worthleychristopher-dev/IC-Test-Fixture-Capstone/docs/eco/ECO_001.pdf

## ENGINEERING CHANGE ORDER (ECO)

ECO NO: 001 APPLIES TO: Reconfigurable Test Fixture (PCB) ECO DATE: 4/30/26
SHEET 1 OF 1

CHANGES:
1. ( Remove ): R9 (CRCW120657K6FKEA) 57.6k ohm resistor.

REASON: Incorrect Value

2. ( Add ): 6490k ohm 1% resistor (0603) to R9.

REASON: Lets circuit produce 4.5 V reference voltage.

Signature: ZF
