worthleychristopher-dev/IC-Test-Fixture-Capstone/docs/eco/ECO_002.pdf

## ENGINEERING CHANGE ORDER (ECO)

ECO NO: 002 APPLIES TO: Reconfigurable Test Fixture (PCB) ECO DATE: 4/30/26
SHEET 1 OF 1

CHANGES:
1. ( | Ignore | ): | Engraved | Reference | Voltage
Values for Vref circuits (U4, U5, U6, U7, U8, TLV431s)

REASON: Incorrect Value Engraved (Reversed Order)

Signature: ZF
