worthleychristopher-dev/IC-Test-Fixture-Capstone/docs/eco/ECO_003.pdf

## ENGINEERING CHANGE ORDER (ECO)

ECO NO: 003 APPLIES TO: Reconfigurable Test Fixture (PCB) ECO DATE: 4/30/26
SHEET 1 OF 1

CHANGES:
1. ( | Ignore | ): | Engraved | positive | polarity
symbol for D3 and D4 (SMF5.0A) components.

REASON: Incorrect polarity orientation engraved.

Signature: ZF
