worthleychristopher-dev/IC-Test-Fixture-Capstone/docs/eco/ECO_004.pdf

## ENGINEERING CHANGE ORDER (ECO)

ECO NO: 004 APPLIES TO: Reconfigurable Test Fixture (PCB) ECO DATE: 4/30/26
SHEET 1 OF 2

CHANGES:
1. ( Add ): Solder 30 gauge AWG jumper wire from USBGND of C1 to GND_ISO of C4

REASON: Isolated circuit unstable without shorted grounds.

Signature: ZF

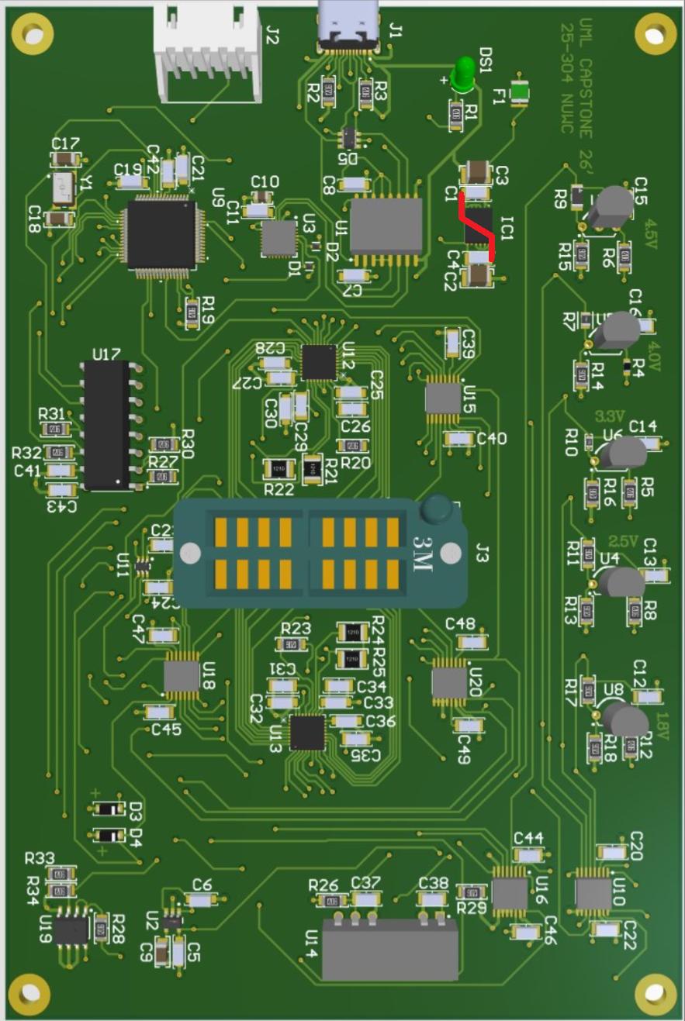
[picture p35: figure]
