worthleychristopher-dev/IC-Test-Fixture-Capstone/docs/eco/ECO_005.pdf

## ENGINEERING CHANGE ORDER (ECO)

ECO NO: 005 APPLIES TO: Reconfigurable Test Fixture (PCB) ECO DATE: 4/30/26
SHEET 1 OF 2

CHANGES:
1. ( Cut ): Traces for pins 6, 7, 10, & 11 of U1 (ADUM4160BRWZ)

REASON: Upstream & Downstream pins routed incorrectly.

2. ( Add ): 30 Gauge AWG jumper wire to connect Pin 3 of D5 to Pin 7 of U1.
3. ( Add ): 30 Gauge AWG jumper wire to connect Pin 4 of D5 to Pin 6 of U1.
4. ( Add ): 30 Gauge AWG jumper wire to connect Pin 10 of U1 to Pin 4 of U3 (CP2102-GM)
5. ( Add ): 30 Gauge AWG jumper wire to connect Pin 11 of U1 to Pin 5 of U3 (CP2102-GM)

REASON: Corrects data pathing for Upstream &
Downstream | pins | of | the | ADUM4160BRWZ | Data
isolator.

Signature: ZF

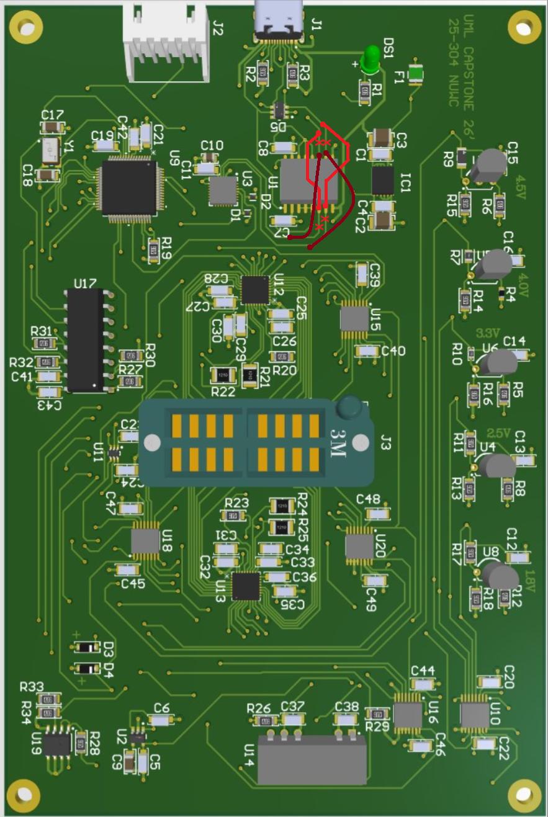
[picture p36: figure]
