worthleychristopher-dev/IC-Test-Fixture-Capstone/docs/images/hardware_images/spice_images/3_3v_TLV431_E192.png

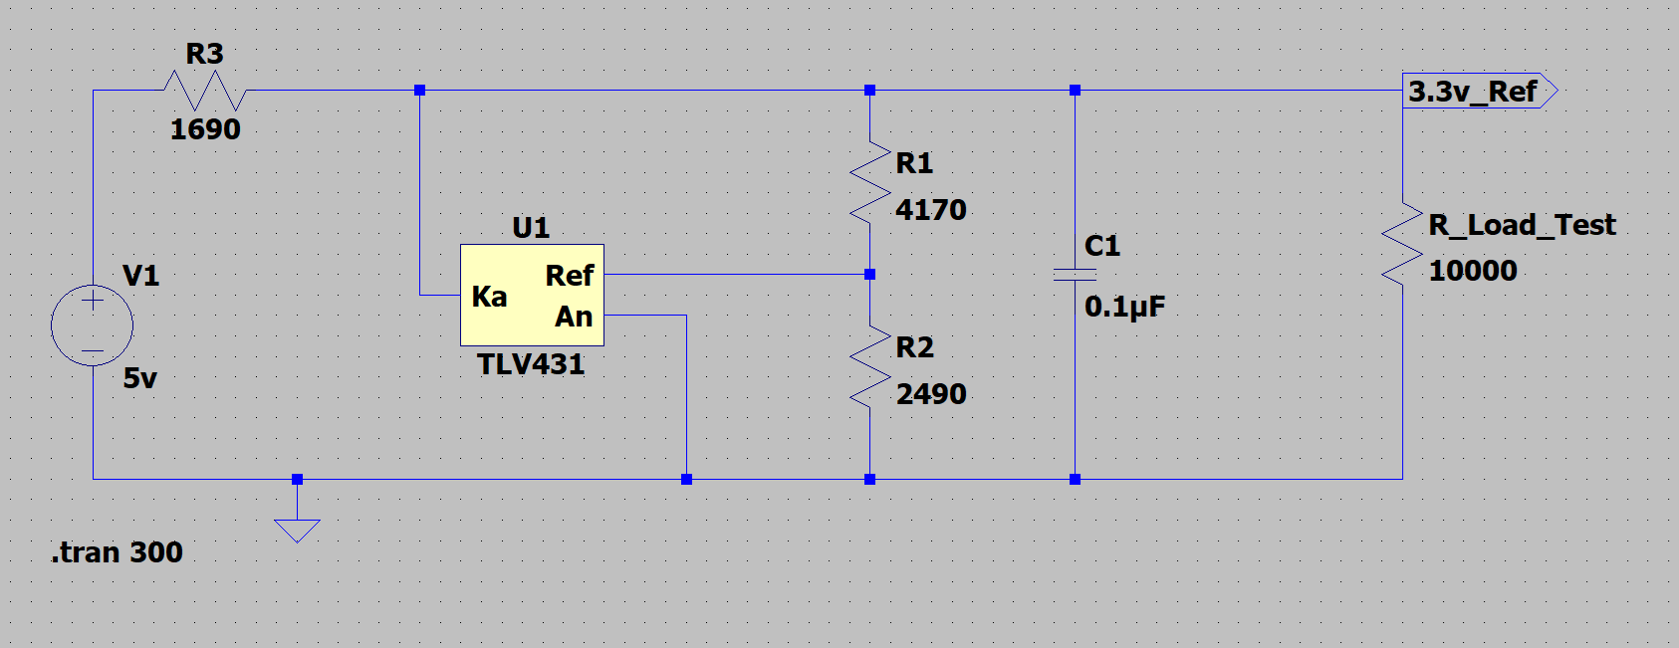
docs/images/hardware_images/spice_images/3_3v_TLV431_E192.png
