worthleychristopher-dev/IC-Test-Fixture-Capstone/docs/images/software_images/flowcharts.png

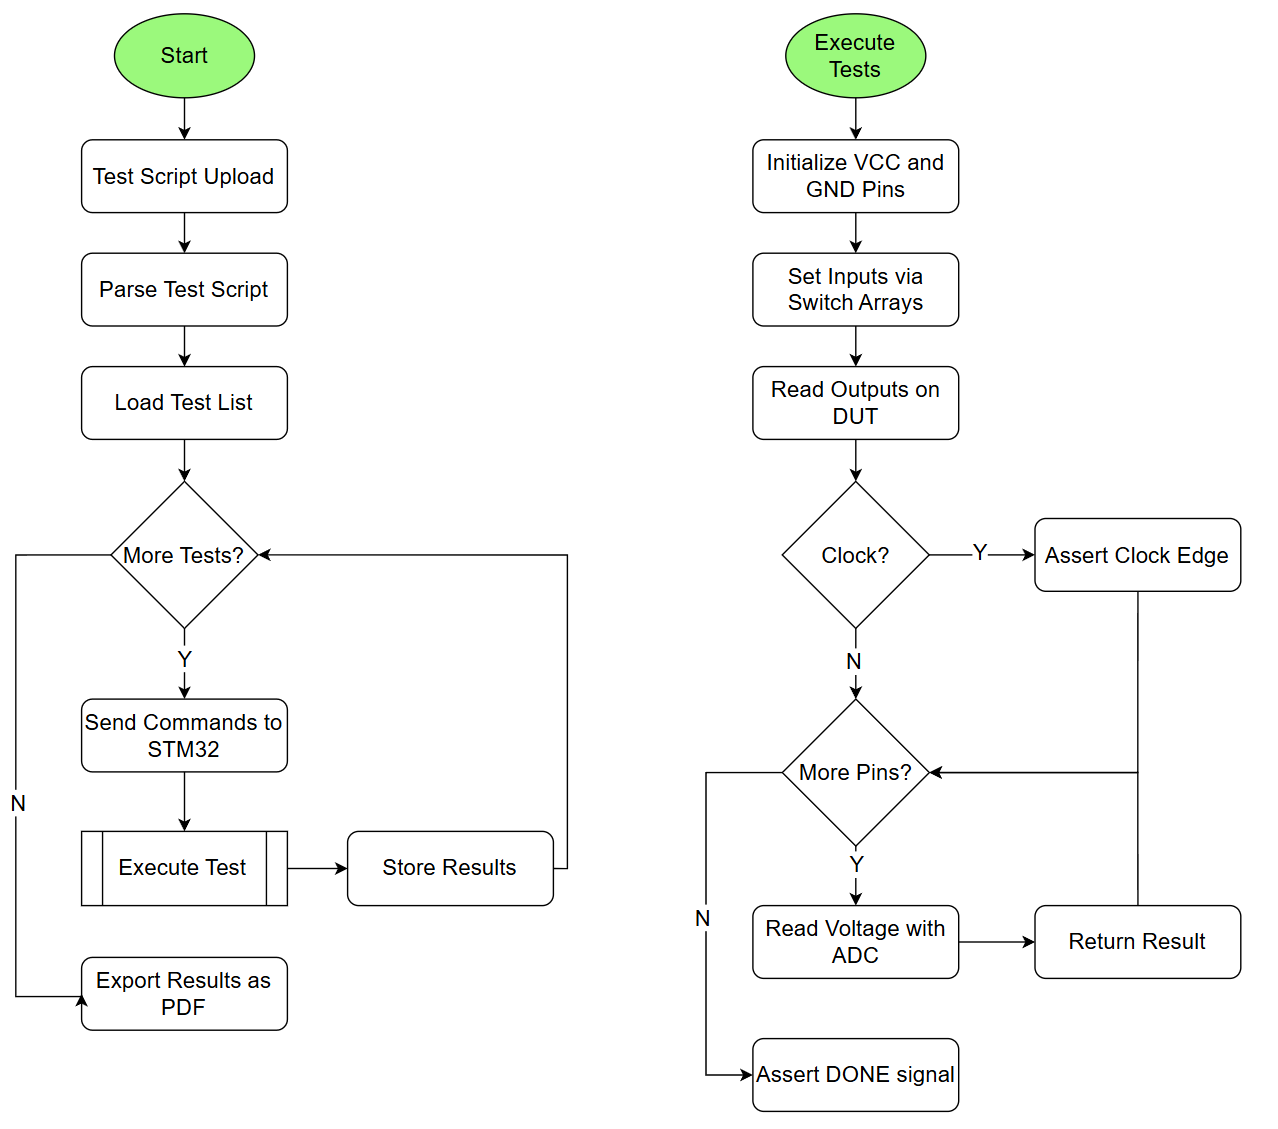
docs/images/software_images/flowcharts.png
