worthleychristopher-dev/IC-Test-Fixture-Capstone/test_results/hct_results/74hct283_short.pdf

## Pin Map

Pin Name | Pin | Pin Name | Pin
S1 | 1 | B1 | 2
A1 | 3 | S0 | 4
A0 | 5 | B0 | 6
CIN | 7 | COUT | 13
S3 | 14 | B3 | 15
A3 | 16 | S2 | 17
A2 | 18 | B2 | 19

## Global Parameters

Parameter | Value
VCC Pin | 20
GND Pin | 8
VCC Voltage | 5
Input Low | 0.8
Input High | 2
Output Low | 0.33
Output High | 3.84

## Tests: IC PASS 12/12

### A=0, B=0, CIN=0 -> S=0: PASS

Inputs | Outputs/Results
A3, A2, A1, A0 | B3, B2, B1, B0 | CIN | COUT | S3 | S2 | S1 | S0
0b0000 | 0b0000 | 0b0 | 0 | 0.0 (0) 0 | | 0.0 (0) 0 | | 0.0 (0) 0 | 0.0 (0) 0 | 0.0 (0)

### A=0, B=0, CIN=1 -> S=1: PASS

Inputs | Outputs/Results
A3, A2, A1, A0 | B3, B2, B1, B0 | CIN | COUT | S3 | S2 | S1 | S0
0b0000 | 0b0000 | 0b1 | 0 | 0.0 (0) 0 | | 0.0 (0) 0 | | 0.0 (0) 0 | 0.0 (0) 1 | 4.86 (1)

### A=1, B=0, CIN=0 -> S=1: PASS

Inputs | Outputs/Results
A3, A2, A1, A0 | B3, B2, B1, B0 | CIN | COUT | S3 | S2 | S1 | S0
0b0001 | 0b0000 | 0b0 | 0 | 0.0 (0) 0 | | 0.0 (0) 0 | | 0.0 (0) 0 | 0.0 (0) 1 | 4.86 (1)

### A=0, B=1, CIN=0 -> S=1: PASS

Inputs | Outputs/Results
A3, A2, A1, A0 | B3, B2, B1, B0 | CIN | COUT | S3 | S2 | S1 | S0
0b0000 | 0b0001 | 0b0 | 0 | 0.0 (0) 0 | | 0.0 (0) 0 | | 0.0 (0) 0 | 0.0 (0) 1 | 4.85 (1)

### A=3, B=5, CIN=0 -> S=8: PASS

Inputs | Outputs/Results
A3, A2, A1, A0 | B3, B2, B1, B0 | CIN | COUT | S3 | S2 | S1 | S0
0b0011 | 0b0101 | 0b0 | 0 | 0.0 (0) 1 | | 4.86 (1) 0 | | 0.0 (0) 0 | 0.0 (0) 0 | 0.0 (0)

### A=15, B=1, CIN=0 -> S=16: PASS

Inputs | Outputs/Results
A3, A2, A1, A0 | B3, B2, B1, B0 | CIN | COUT | S3 | S2 | S1 | S0
0b1111 | 0b0001 | 0b0 | 1 | 4.85 (1) 0 | | 0.0 (0) 0 | | 0.0 (0) 0 | 0.0 (0) 0 | 0.0 (0)

### A=15, B=15, CIN=0 -> S=30: PASS

Inputs | Outputs/Results
A3, A2, A1, A0 | B3, B2, B1, B0 | CIN | COUT | S3 | S2 | S1 | S0
0b1111 | 0b1111 | 0b0 | 1 | 4.85 (1) 1 | | 4.85 (1) 1 | | 4.85 (1) 1 | 4.85 (1) 0 | 0.0 (0)

### A=15, B=15, CIN=1 -> S=31: PASS

Inputs | Outputs/Results
A3, A2, A1, A0 | B3, B2, B1, B0 | CIN | COUT | S3 | S2 | S1 | S0
0b1111 | 0b1111 | 0b1 | 1 | 4.85 (1) 1 | | 4.85 (1) 1 | | 4.85 (1) 1 | 4.85 (1) 1 | 4.85 (1)

### A=10, B=5, CIN=0 -> S=15: PASS

Inputs | Outputs/Results
A3, A2, A1, A0 | B3, B2, B1, B0 | CIN | COUT | S3 | S2 | S1 | S0
0b1010 | 0b0101 | 0b0 | 0 | 0.0 (0) 1 | | 4.86 (1) 1 | | 4.85 (1) 1 | 4.85 (1) 1 | 4.85 (1)

### A=10, B=10, CIN=1 -> S=21: PASS

Inputs | Outputs/Results
A3, A2, A1, A0 | B3, B2, B1, B0 | CIN | COUT | S3 | S2 | S1 | S0
0b1010 | 0b1010 | 0b1 | 1 | 4.85 (1) 0 | | 0.0 (0) 1 | | 4.85 (1) 0 | 0.0 (0) 1 | 4.85 (1)

### A=7, B=1, CIN=0 -> S=21: PASS

Inputs | Outputs/Results
A3, A2, A1, A0 | B3, B2, B1, B0 | CIN | COUT | S3 | S2 | S1 | S0
0b0111 | 0b0001 | 0b0 | 0 | 0.0 (0) 1 | | 4.86 (1) 0 | | 0.0 (0) 0 | 0.0 (0) 0 | 0.0 (0)

### A=7, B=3, CIN=1 -> S=21: PASS

Inputs | Outputs/Results
A3, A2, A1, A0 | B3, B2, B1, B0 | CIN | COUT | S3 | S2 | S1 | S0
0b1100 | 0b0011 | 0b1 | 1 | 4.86 (1) 0 | | 0.0 (0) 0 | | 0.0 (0) 0 | 0.0 (0) 0 | 0.0 (0)
