worthleychristopher-dev/IC-Test-Fixture-Capstone/test_results/hct_results/74hct374.pdf

## Pin Map

Pin Name | Pin | Pin Name | Pin
OE | 1 | 1Q | 2
1D | 3 | 2D | 4
2Q | 5 | 3Q | 6
3D | 7 | 4D | 8
4Q | 9 | CLK | 11
5Q | 12 | 5D | 13
6D | 14 | 6Q | 15
7Q | 16 | 7D | 17
8D | 18 | 8Q | 19

## Global Parameters

Parameter | Value
VCC Pin | 20
GND Pin | 10
VCC Voltage | 5
Input Low | 0.8
Input High | 2
Output Low | 0.33
Output High | 3.84

## Tests: IC PASS 16/16

### Flip-Flop 1: PASS

Inputs | Outputs/Results
OE | 1D | CLK | 1Q
L | H | R | H | 4.85 (H)
L | L | R | L | 0.0 (L)
H | X | X | Z | 1.59 (Z)

### Flip-Flop 1 No Change: PASS

Inputs | Outputs/Results
OE | 1D | CLK | 1Q
L | H | R | H | 4.85 (H)
L | H | L | H | 4.85 (H)
L | L | R | L | 0.0 (L)
L | L | L | L | 0.0 (L)

### Flip-Flop 2: PASS

Inputs | Outputs/Results
OE | 2D | CLK | 2Q
L | H | R | H | 4.85 (H)
L | L | R | L | 0.0 (L)
H | X | X | Z | 1.59 (Z)

### Flip-Flop 2 No Change: PASS

Inputs | Outputs/Results
OE | 2D | CLK | 2Q
L | H | R | H | 4.85 (H)
L | H | L | H | 4.85 (H)
L | L | R | L | 0.0 (L)
L | L | L | L | 0.0 (L)

### Flip-Flop 3: PASS

Inputs | Outputs/Results
OE | 3D | CLK | 3Q
L | H | R | H | 4.85 (H)
L | L | R | L | 0.0 (L)
H | X | X | Z | 1.59 (Z)

### Flip-Flop 3 No Change: PASS

Inputs | Outputs/Results
OE | 3D | CLK | 3Q
L | H | R | H | 4.85 (H)
L | H | L | H | 4.85 (H)
L | L | R | L | 0.0 (L)
L | L | L | L | 0.0 (L)

### Flip-Flop 4: PASS

Inputs | Outputs/Results
OE | 4D | CLK | 4Q
L | H | R | H | 4.85 (H)
L | L | R | L | 0.0 (L)
H | X | X | Z | 1.59 (Z)

### Flip-Flop 4 No Change: PASS

Inputs | Outputs/Results
OE | 4D | CLK | 4Q
L | H | R | H | 4.85 (H)
L | H | L | H | 4.85 (H)
L | L | R | L | 0.0 (L)
L | L | L | L | 0.0 (L)

### Flip-Flop 5: PASS

Inputs | Outputs/Results
OE | 5D | CLK | 5Q
L | H | R | H | 4.85 (H)
L | L | R | L | 0.0 (L)
H | X | X | Z | 1.59 (Z)

### Flip-Flop 5 No Change: PASS

Inputs | Outputs/Results
OE | 5D | CLK | 5Q
L | H | R | H | 4.85 (H)
L | H | L | H | 4.85 (H)
L | L | R | L | 0.0 (L)
L | L | L | L | 0.0 (L)

### Flip-Flop 6: PASS

Inputs | Outputs/Results
OE | 6D | CLK | 6Q
L | H | R | H | 4.85 (H)
L | L | R | L | 0.0 (L)
H | X | X | Z | 1.59 (Z)

### Flip-Flop 6 No Change: PASS

Inputs | Outputs/Results
OE | 6D | CLK | 6Q
L | H | R | H | 4.85 (H)
L | H | L | H | 4.85 (H)
L | L | R | L | 0.0 (L)
L | L | L | L | 0.0 (L)

### Flip-Flop 7: PASS

Inputs | Outputs/Results
OE | 7D | CLK | 7Q
L | H | R | H | 4.85 (H)
L | L | R | L | 0.0 (L)
H | X | X | Z | 1.59 (Z)

### Flip-Flop 7 No Change: PASS

Inputs | Outputs/Results
OE | 7D | CLK | 7Q
L | H | R | H | 4.85 (H)
L | H | L | H | 4.85 (H)
L | L | R | L | 0.0 (L)
L | L | L | L | 0.0 (L)

### Flip-Flop 8: PASS

Inputs | Outputs/Results
OE | 8D | CLK | 8Q
L | H | R | H | 4.85 (H)
L | L | R | L | 0.0 (L)
H | X | X | Z | 1.59 (Z)

### Flip-Flop 8 No Change: PASS

Inputs | Outputs/Results
OE | 8D | CLK | 8Q
L | H | R | H | 4.85 (H)
L | H | L | H | 4.85 (H)
L | L | R | L | 0.0 (L)
L | L | L | L | 0.0 (L)
