worthleychristopher-dev/IC-Test-Fixture-Capstone/test_results/hct_results/74hct688_short.pdf

## Pin Map

Pin Name | Pin | Pin Name | Pin
E | 1 | A0 | 2
A1 | 4 | A2 | 6
A3 | 8 | A4 | 11
A5 | 13 | A6 | 15
A7 | 17 | B0 | 3
B1 | 5 | B2 | 7
B3 | 9 | B4 | 12
B5 | 14 | B6 | 16
B7 | 18 | Y | 19

## Global Parameters

Parameter | Value
VCC Pin | 20
GND Pin | 10
VCC Voltage | 5
Input Low | 0.8
Input High | 2
Output Low | 0.33
Output High | 3.84

## Tests: IC PASS 19/19

### Comparator Disabled: PASS

Inputs | Outputs/Results
E | A7, A6, A5, A4, A3, A2, A1, A0 | B7, B6, B5, B4, B3, B2, B1, B0 | Y
H | 0b00000000 | 0b00000000 | H | 4.85 (H)

### A=0, B=1 -> Y=H: PASS

Inputs | Outputs/Results
E | A7, A6, A5, A4, A3, A2, A1, A0 | B7, B6, B5, B4, B3, B2, B1, B0 | Y
L | 0b00000000 | 0b00000001 | H | 4.85 (H)

### A=0, B=0 -> Y=L: PASS

Inputs | Outputs/Results
E | A7, A6, A5, A4, A3, A2, A1, A0 | B7, B6, B5, B4, B3, B2, B1, B0 | Y
L | 0b00000000 | 0b00000000 | L | 0.0 (L)

### A=2, B=1 -> Y=H: PASS

Inputs | Outputs/Results
E | A7, A6, A5, A4, A3, A2, A1, A0 | B7, B6, B5, B4, B3, B2, B1, B0 | Y
L | 0b00000010 | 0b00000001 | H | 4.85 (H)

### A=2, B=2 -> Y=L: PASS

Inputs | Outputs/Results
E | A7, A6, A5, A4, A3, A2, A1, A0 | B7, B6, B5, B4, B3, B2, B1, B0 | Y
L | 0b00000010 | 0b00000010 | L | 0.0 (L)

### A=2, B=4 -> Y=H: PASS

Inputs | Outputs/Results
E | A7, A6, A5, A4, A3, A2, A1, A0 | B7, B6, B5, B4, B3, B2, B1, B0 | Y
L | 0b00000010 | 0b00000100 | H | 4.85 (H)

### A=4, B=4 -> Y=L: PASS

Inputs | Outputs/Results
E | A7, A6, A5, A4, A3, A2, A1, A0 | B7, B6, B5, B4, B3, B2, B1, B0 | Y
L | 0b00000100 | 0b00000100 | L | 0.0 (L)

### A=6, B=8 -> Y=H: PASS

Inputs | Outputs/Results
E | A7, A6, A5, A4, A3, A2, A1, A0 | B7, B6, B5, B4, B3, B2, B1, B0 | Y
L | 0b00000110 | 0b00001000 | H | 4.85 (H)

### A=8, B=8 -> Y=L: PASS

Inputs | Outputs/Results
E | A7, A6, A5, A4, A3, A2, A1, A0 | B7, B6, B5, B4, B3, B2, B1, B0 | Y
L | 0b00001000 | 0b00001000 | L | 0.0 (L)

### A=16, B=12 -> Y=H: PASS

Inputs | Outputs/Results
E | A7, A6, A5, A4, A3, A2, A1, A0 | B7, B6, B5, B4, B3, B2, B1, B0 | Y
L | 0b00010000 | 0b00001100 | H | 4.85 (H)

### A=16, B=16 -> Y=L: PASS

Inputs | Outputs/Results
E | A7, A6, A5, A4, A3, A2, A1, A0 | B7, B6, B5, B4, B3, B2, B1, B0 | Y
L | 0b00010000 | 0b00010000 | L | 0.0 (L)

### A=31, B=32 -> Y=H: PASS

Inputs | Outputs/Results
E | A7, A6, A5, A4, A3, A2, A1, A0 | B7, B6, B5, B4, B3, B2, B1, B0 | Y
L | 0b00011111 | 0b00100000 | H | 4.85 (H)

### A=32, B=32 -> Y=L: PASS

Inputs | Outputs/Results
E | A7, A6, A5, A4, A3, A2, A1, A0 | B7, B6, B5, B4, B3, B2, B1, B0 | Y
L | 0b00100000 | 0b00100000 | L | 0.0 (L)

### A=32, B=64 -> Y=H: PASS

Inputs | Outputs/Results
E | A7, A6, A5, A4, A3, A2, A1, A0 | B7, B6, B5, B4, B3, B2, B1, B0 | Y
L | 0b00100000 | 0b01000000 | H | 4.85 (H)

### A=64, B=64 -> Y=L: PASS

Inputs | Outputs/Results
E | A7, A6, A5, A4, A3, A2, A1, A0 | B7, B6, B5, B4, B3, B2, B1, B0 | Y
L | 0b01000000 | 0b01000000 | L | 0.0 (L)

### A=11, B=128 -> Y=H: PASS

Inputs | Outputs/Results
E | A7, A6, A5, A4, A3, A2, A1, A0 | B7, B6, B5, B4, B3, B2, B1, B0 | Y
L | 0b00001011 | 0b10000000 | H | 4.85 (H)

### A=128, B=128 -> Y=H: PASS

Inputs | Outputs/Results
E | A7, A6, A5, A4, A3, A2, A1, A0 | B7, B6, B5, B4, B3, B2, B1, B0 | Y
L | 0b10000000 | 0b10000000 | L | 0.0 (L)

### A=255, B=254 -> Y=H: PASS

Inputs | Outputs/Results
E | A7, A6, A5, A4, A3, A2, A1, A0 | B7, B6, B5, B4, B3, B2, B1, B0 | Y
L | 0b11111111 | 0b11111110 | H | 4.85 (H)

### A=170, B=85 -> Y=H: PASS

Inputs | Outputs/Results
E | A7, A6, A5, A4, A3, A2, A1, A0 | B7, B6, B5, B4, B3, B2, B1, B0 | Y
L | 0b10101010 | 0b01010101 | H | 4.85 (H)
