worthleychristopher-dev/IC-Test-Fixture-Capstone/test_results/hct_results/74hct74.pdf

## Pin Map

Pin Name | Pin | Pin Name | Pin
1CLR | 1 | 1D | 2
1CLK | 3 | 1PRE | 4
1Q | 5 | 1Qnot | 6
2Qnot | 14 | 2Q | 15
2PRE | 16 | 2CLK | 17
2D | 18 | 2CLR | 19

## Global Parameters

Parameter | Value
VCC Pin | 20
GND Pin | 7
VCC Voltage | 5
Input Low | 0.8
Input High | 2
Output Low | 0.33
Output High | 3.84

## Tests: IC PASS 4/4

### D Flip-Flop 1: PASS

Inputs | Outputs/Results
1PRE | 1CLR | 1D | 1CLK | 1Q | 1Qnot
L | H | X | X | H | 4.81 (H) L | 0.02 (L)
H | L | X | X | L | 0.2 (L) H | 4.43 (H)
L | L | X | X | H | 4.34 (H) H | 4.39 (H)
H | H | H | R | H | 4.81 (H) L | 0.02 (L)
H | H | L | R | L | 0.02 (L) H | 4.82 (H)

### D Flip-Flop 2: PASS

Inputs | Outputs/Results
2PRE | 2CLR | 2D | 2CLK | 2Q | 2Qnot
L | H | X | X | H | 4.79 (H) L | 0.08 (L)
H | L | X | X | L | 0.19 (L) H | 4.34 (H)
L | L | X | X | H | 4.38 (H) H | 4.27 (H)
H | H | H | R | H | 4.8 (H) L | 0.03 (L)
H | H | L | R | L | 0.03 (L) H | 4.81 (H)

### No Change -> H: PASS

Inputs | Outputs/Results
1PRE, 2PRE | 1CLR, 2CLR | 1D, 2D | 1CLK, 2CLK | 1Q | 2Q | 1Qnot | 2Qnot
H | H | H | R | H | 4.85 (H) H | | 4.85 (H) L | 0.0 (L) L | 0.0 (L)
H | H | X | L | H | 4.86 (H) H | | 4.86 (H) L | 0.0 (L) L | 0.0 (L)

### No Change -> L: PASS

Inputs | Outputs/Results
1PRE, 2PRE | 1CLR, 2CLR | 1D, 2D | 1CLK, 2CLK | 1Q | 2Q | 1Qnot | 2Qnot
H | H | L | R | L | 0.0 (L) L | | 0.0 (L) H | 4.85 (H) H | 4.85 (H)
H | H | X | L | L | 0.0 (L) L | | 0.0 (L) H | 4.86 (H) H | 4.86 (H)
