worthleychristopher-dev/IC-Test-Fixture-Capstone/test_results/hc_results/74hc04.pdf

## Global Parameters

Parameter | Value
VCC Pin | 20
GND Pin | 7
VCC Voltage | 2.5, 3.3, 4.0, 4.5, 5
Input Low | 0.75, 0.99, 1.2, 1.35, 1.5
Input High | 1.75, 2.31, 2.8, 3.15, 3.5
Output Low | 0.3, 0.3, 0.3, 0.3, 0.3
Output High | 2.2, 3.0, 3.6, 4.1, 4.7

## Tests: IC PASS 2/2

### A=L -> Y=H: PASS

Inputs | VCC | Outputs/Results
1, 3, 5, 15, 17, 19 | | 2 | 4 | 6 | 14 | 16 | 18
L | 2.5 | H | 2.37 (H) | H | 2.37 (H) | H | 2.37 (H) | H | 2.37 (H) | H | 2.37 (H) | H | 2.37 (H)
| 3.3 | | 3.15 (H) | | 3.15 (H) | | 3.15 (H) | | 3.15 (H) | | 3.15 (H) | | 3.15 (H)
| 4.0 | | 3.81 (H) | | 3.81 (H) | | 3.81 (H) | | 3.81 (H) | | 3.81 (H) | | 3.81 (H)
| 4.5 | | 4.43 (H) | | 4.43 (H) | | 4.43 (H) | | 4.43 (H) | | 4.43 (H) | | 4.43 (H)
| 5 | | 4.87 (H) | | 4.87 (H) | | 4.87 (H) | | 4.87 (H) | | 4.87 (H) | | 4.87 (H)

### A=H -> Y=L: PASS

Inputs | VCC | Outputs/Results
1, 3, 5, 15, 17, 19 | | 2 | 4 | 6 | 14 | 16 | 18
H | 2.5 | L | 0.0 (L) | L | 0.0 (L) | L | 0.0 (L) | L | 0.0 (L) | L | 0.0 (L) | L | 0.0 (L)
| 3.3 | | 0.0 (L) | | 0.0 (L) | | 0.0 (L) | | 0.0 (L) | | 0.0 (L) | | 0.0 (L)
| 4.0 | | 0.0 (L) | | 0.0 (L) | | 0.0 (L) | | 0.0 (L) | | 0.0 (L) | | 0.0 (L)
| 4.5 | | 0.0 (L) | | 0.0 (L) | | 0.0 (L) | | 0.0 (L) | | 0.0 (L) | | 0.0 (L)
| 5 | | 0.0 (L) | | 0.0 (L) | | 0.0 (L) | | 0.0 (L) | | 0.0 (L) | | 0.0 (L)
