worthleychristopher-dev/IC-Test-Fixture-Capstone/test_results/hct_results/74hct04.pdf

## Global Parameters

Parameter | Value
VCC Pin | 20
GND Pin | 7
VCC Voltage | 5
Input Low | 0.8
Input High | 2
Output Low | 0.33
Output High | 3.84

## Tests: IC PASS 2/2

### A=L -> Y=H: PASS

Inputs | Outputs/Results
1, 3, 5, 15, 17, 19 | 2 | 4 | 6 | 14 | 16 | 18
L | H | 4.87 (H) H | | 4.87 (H) H | | 4.87 (H) H | 4.87 (H) H | 4.87 (H) H | 4.87 (H)

### A=H -> Y=L: PASS

Inputs | Outputs/Results
1, 3, 5, 15, 17, 19 | 2 | 4 | 6 | 14 | 16 | 18
H | L | 0.0 (L) L | | 0.0 (L) L | | 0.0 (L) L | 0.0 (L) L | 0.0 (L) L | 0.0 (L)
