worthleychristopher-dev/IC-Test-Fixture-Capstone/test_results/hct_results/74hct08.pdf

## Global Parameters

Parameter | Value
VCC Pin | 20
GND Pin | 7
VCC Voltage | 5
Input Low | 0.8
Input High | 2
Output Low | 0.33
Output High | 3.84

## Tests: IC PASS 4/4

### A=L, B=L -> Y=L: PASS

Inputs | Outputs/Results
1, 4, 15, 18 | 2, 5, 16, 19 | 3 | 6 | 14 | 17
L | L | L | 0.0 (L) L | | 0.0 (L) L | 0.0 (L) L | 0.0 (L)

### A=L, B=H -> Y=L: PASS

Inputs | Outputs/Results
1, 4, 15, 18 | 2, 5, 16, 19 | 3 | 6 | 14 | 17
L | H | L | 0.0 (L) L | | 0.0 (L) L | 0.0 (L) L | 0.0 (L)

### A=H, B=L -> Y=L: PASS

Inputs | Outputs/Results
1, 4, 15, 18 | 2, 5, 16, 19 | 3 | 6 | 14 | 17
H | L | L | 0.0 (L) L | | 0.0 (L) L | 0.0 (L) L | 0.0 (L)

### A=H, B=H -> Y=H: PASS

Inputs | Outputs/Results
1, 4, 15, 18 | 2, 5, 16, 19 | 3 | 6 | 14 | 17
H | H | H | 4.87 (H) H | | 4.87 (H) H | 4.87 (H) H | 4.87 (H)
