worthleychristopher-dev/IC-Test-Fixture-Capstone/test_results/hct_results/74hct138.pdf

## Pin Map

Pin Name | Pin | Pin Name | Pin
A | 1 | B | 2
C | 3 | G2A | 4
G2B | 5 | G1 | 6
Y7 | 7 | Y6 | 13
Y5 | 14 | Y4 | 15
Y3 | 16 | Y2 | 17
Y1 | 18 | Y0 | 19

## Global Parameters

Parameter | Value
VCC Pin | 20
GND Pin | 8
VCC Voltage | 5
Input Low | 0.8
Input High | 2
Output Low | 0.33
Output High | 3.84

## Tests: IC PASS 11/11

### Active Low G2A: PASS

Inputs | Outputs/Results
G1, G2A, G2B | C, B, A | Y0 | Y1 | Y2 | Y3 | Y4 | Y5 | Y6 | Y7
X, H, X | X, X, X | H | 4.87 (H) H | | 4.87 (H) H | | 4.87 (H) H | | 4.87 (H) H | 4.87 (H) H | 4.87 (H) H | 4.87 (H) H | 4.87 (H)

### Active Low G2B: PASS

Inputs | Outputs/Results
G1, G2A, G2B | C, B, A | Y0 | Y1 | Y2 | Y3 | Y4 | Y5 | Y6 | Y7
X, X, H | X, X, X | H | 4.87 (H) H | | 4.87 (H) H | | 4.87 (H) H | | 4.87 (H) H | 4.87 (H) H | 4.87 (H) H | 4.87 (H) H | 4.87 (H)

### Low G1: PASS

Inputs | Outputs/Results
G1, G2A, G2B | C, B, A | Y0 | Y1 | Y2 | Y3 | Y4 | Y5 | Y6 | Y7
L, X, X | X, X, X | H | 4.87 (H) H | | 4.87 (H) H | | 4.87 (H) H | | 4.87 (H) H | 4.87 (H) H | 4.87 (H) H | 4.87 (H) H | 4.87 (H)

### Output Y0: PASS

Inputs | Outputs/Results
G1, G2A, G2B | C, B, A | Y0 | Y1 | Y2 | Y3 | Y4 | Y5 | Y6 | Y7
H, L, L | 0b000 | L | 0.0 (L) H | | 4.87 (H) H | | 4.87 (H) H | | 4.87 (H) H | 4.87 (H) H | 4.87 (H) H | 4.87 (H) H | 4.87 (H)

### Output Y1: PASS

Inputs | Outputs/Results
G1, G2A, G2B | C, B, A | Y0 | Y1 | Y2 | Y3 | Y4 | Y5 | Y6 | Y7
H, L, L | 0b001 | H | 4.87 (H) L | | 0.0 (L) H | | 4.87 (H) H | | 4.87 (H) H | 4.87 (H) H | 4.87 (H) H | 4.87 (H) H | 4.87 (H)

### Output Y2: PASS

Inputs | Outputs/Results
G1, G2A, G2B | C, B, A | Y0 | Y1 | Y2 | Y3 | Y4 | Y5 | Y6 | Y7
H, L, L | 0b010 | H | 4.87 (H) H | | 4.87 (H) L | | 0.0 (L) H | | 4.87 (H) H | 4.87 (H) H | 4.87 (H) H | 4.87 (H) H | 4.87 (H)

### Output Y3: PASS

Inputs | Outputs/Results
G1, G2A, G2B | C, B, A | Y0 | Y1 | Y2 | Y3 | Y4 | Y5 | Y6 | Y7
H, L, L | 0b011 | H | 4.87 (H) H | | 4.87 (H) H | | 4.87 (H) L | | 0.0 (L) H | 4.87 (H) H | 4.87 (H) H | 4.87 (H) H | 4.87 (H)

### Output Y4: PASS

Inputs | Outputs/Results
G1, G2A, G2B | C, B, A | Y0 | Y1 | Y2 | Y3 | Y4 | Y5 | Y6 | Y7
H, L, L | 0b100 | H | 4.87 (H) H | | 4.87 (H) H | | 4.87 (H) H | | 4.87 (H) L | 0.0 (L) H | 4.87 (H) H | 4.87 (H) H | 4.87 (H)

### Output Y5: PASS

Inputs | Outputs/Results
G1, G2A, G2B | C, B, A | Y0 | Y1 | Y2 | Y3 | Y4 | Y5 | Y6 | Y7
H, L, L | 0b101 | H | 4.87 (H) H | | 4.87 (H) H | | 4.87 (H) H | | 4.87 (H) H | 4.87 (H) L | 0.0 (L) H | 4.87 (H) H | 4.87 (H)

### Output Y6: PASS

Inputs | Outputs/Results
G1, G2A, G2B | C, B, A | Y0 | Y1 | Y2 | Y3 | Y4 | Y5 | Y6 | Y7
H, L, L | 0b110 | H | 4.87 (H) H | | 4.87 (H) H | | 4.87 (H) H | | 4.87 (H) H | 4.87 (H) H | 4.87 (H) L | 0.0 (L) H | 4.87 (H)

### Output Y7: PASS

Inputs | Outputs/Results
G1, G2A, G2B | C, B, A | Y0 | Y1 | Y2 | Y3 | Y4 | Y5 | Y6 | Y7
H, L, L | 0b111 | H | 4.87 (H) H | | 4.87 (H) H | | 4.87 (H) H | | 4.87 (H) H | 4.87 (H) H | 4.87 (H) H | 4.87 (H) L | 0.0 (L)
