worthleychristopher-dev/IC-Test-Fixture-Capstone/test_results/hct_results/74hct153.pdf

## Pin Map

Pin Name | Pin | Pin Name | Pin
1E | 1 | S1 | 2
1I3 | 3 | 1I2 | 4
1I1 | 5 | 1I0 | 6
1Y | 7 | 2Y | 13
2I0 | 14 | 2I1 | 15
2I2 | 16 | 2I3 | 17
S0 | 18 | 2E | 19

## Global Parameters

Parameter | Value
VCC Pin | 20
GND Pin | 8
VCC Voltage | 5
Input Low | 0.8
Input High | 2
Output Low | 0.33
Output High | 3.84

## Tests: IC PASS 2/2

### Mux 1: PASS

Inputs | Outputs/Results
1E | S1 | S0 | 1I3 | 1I2 | 1I1 | 1I0 | 1Y
H | X | X | X | X | X | X | L | 0.0 (L)
L | L | L | X | X | X | L | L | 0.0 (L)
L | L | L | X | X | X | H | H | 4.87 (H)
L | L | H | X | X | L | X | L | 0.0 (L)
L | L | H | X | X | H | X | H | 4.87 (H)
L | H | L | X | L | X | X | L | 0.0 (L)

Inputs | Outputs/Results
1E | S1 | S0 | 1I3 | 1I2 | 1I1 | 1I0 | 1Y
L | H | L | X | H | X | X | H | 4.87 (H)
L | H | H | L | X | X | X | L | 0.0 (L)
L | H | H | H | X | X | X | H | 4.87 (H)

### Mux 2: PASS

Inputs | Outputs/Results
2E | S1 | S0 | 2I3 | 2I2 | 2I1 | 2I0 | 2Y
H | X | X | X | X | X | X | L | 0.0 (L)
L | L | L | X | X | X | L | L | 0.0 (L)
L | L | L | X | X | X | H | H | 4.87 (H)
L | L | H | X | X | L | X | L | 0.0 (L)
L | L | H | X | X | H | X | H | 4.87 (H)
L | H | L | X | L | X | X | L | 0.0 (L)
L | H | L | X | H | X | X | H | 4.87 (H)
L | H | H | L | X | X | X | L | 0.0 (L)
L | H | H | H | X | X | X | H | 4.87 (H)
