worthleychristopher-dev/IC-Test-Fixture-Capstone/test_results/hct_results/74hct244.pdf

## Global Parameters

Parameter | Value
VCC Pin | 20
GND Pin | 10
VCC Voltage | 5
Input Low | 0.8
Input High | 2
Output Low | 0.4
Output High | 3.7

## Tests: IC PASS 6/6

### Buffer 1 Disabled: PASS

Inputs | Outputs/Results
1 | 2, 4, 6, 8 | 18 | 16 | 14 | 12
H | X | Z | 1.59 (Z) Z | | 1.59 (Z) Z | 1.59 (Z) Z | 1.59 (Z)

### Buffer 1 A=L -> Y=L: PASS

Inputs | Outputs/Results
1 | 2, 4, 6, 8 | 18 | 16 | 14 | 12
L | L | L | 0.0 (L) L | | 0.0 (L) L | 0.0 (L) L | 0.0 (L)

### Buffer 1 A=H -> Y=H: PASS

Inputs | Outputs/Results
1 | 2, 4, 6, 8 | 18 | 16 | 14 | 12
L | H | H | 4.87 (H) H | | 4.87 (H) H | 4.87 (H) H | 4.87 (H)

### Buffer 2 Disabled: PASS

Inputs | Outputs/Results
19 | 11, 13, 15, 17 | 9 | 7 | 5 | 3
H | X | Z | 1.59 (Z) Z | | 1.59 (Z) Z | 1.59 (Z) Z | 1.59 (Z)

### Buffer 2 A=L -> Y=L: PASS

Inputs | Outputs/Results
19 | 11, 13, 15, 17 | 9 | 7 | 5 | 3
L | L | L | 0.0 (L) L | | 0.0 (L) L | 0.0 (L) L | 0.0 (L)

### Buffer 2 A=H -> Y=H: PASS

Inputs | Outputs/Results
19 | 11, 13, 15, 17 | 9 | 7 | 5 | 3
L | H | H | 4.87 (H) H | | 4.87 (H) H | 4.87 (H) H | 4.87 (H)
