worthleychristopher-dev/IC-Test-Fixture-Capstone/test_results/hc_results/74hc245_short.pdf

## Pin Map

Pin Name | Pin | Pin Name | Pin
DIR | 1 | OE | 19
A1 | 2 | A2 | 3
A3 | 4 | A4 | 5
A5 | 6 | A6 | 7
A7 | 8 | A8 | 9
B1 | 18 | B2 | 17
B3 | 16 | B4 | 15
B5 | 14 | B6 | 13
B7 | 12 | B8 | 11

## Global Parameters

Parameter | Value
VCC Pin | 20
GND Pin | 10
VCC Voltage | 2.5, 3.3, 4.0, 4.5, 5
Input Low | 0.75, 0.99, 1.2, 1.35, 1.5
Input High | 1.75, 2.31, 2.8, 3.15, 3.5
Output Low | 0.3, 0.3, 0.3, 0.3, 0.3
Output High | 2.2, 3.0, 3.6, 4.1, 4.7

## Tests: IC PASS 19/19

### A=0, DIR=H, OE=L -> B=0: PASS

Inputs | VCC | Outputs/Results
A8, A7, A6, A5, A4, A3, A2, A1 | DIR | OE | | B8 | B7 | B6 | B5 | B4 | B3 | B2 | B1
0b00000000 | H | L | 2.5 | 0 | 0.0 (0) | 0 | 0.0 (0) | 0 | 0.0 (0) | 0 | 0.0 (0) | 0 | 0.0 (0) | 0 | 0.0 (0) | 0 | 0.0 (0) | 0 | 0.0 (0)
| | | 3.3 | | 0.0 (0) | | 0.0 (0) | | 0.0 (0) | | 0.0 (0) | | 0.0 (0) | | 0.0 (0) | | 0.0 (0) | | 0.0 (0)
| | | 4.0 | | 0.0 (0) | | 0.0 (0) | | 0.0 (0) | | 0.0 (0) | | 0.0 (0) | | 0.0 (0) | | 0.0 (0) | | 0.0 (0)
| | | 4.5 | | 0.0 (0) | | 0.0 (0) | | 0.0 (0) | | 0.0 (0) | | 0.0 (0) | | 0.0 (0) | | 0.0 (0) | | 0.0 (0)
| | | 5 | | 0.0 (0) | | 0.0 (0) | | 0.0 (0) | | 0.0 (0) | | 0.0 (0) | | 0.0 (0) | | 0.0 (0) | | 0.0 (0)

### A=1, DIR=H, OE=L -> B=1: PASS

Inputs | VCC | Outputs/Results
A8, A7, A6, A5, A4, A3, A2, A1 | DIR | OE | | B8 | B7 | B6 | B5 | B4 | B3 | B2 | B1
0b00000001 | H | L | 2.5 | 0 | 0.0 (0) | 0 | 0.0 (0) | 0 | 0.0 (0) | 0 | 0.0 (0) | 0 | 0.0 (0) | 0 | 0.0 (0) | 0 | 0.0 (0) | 1 | 2.37 (1)
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
5 | | 0.0 (0) | | 0.0 (0) | | 0.0 (0) | | 0.0 (0) | | 0.0 (0) | | 0.0 (0) | | 0.0 (0) | | 0.0 (0) | | 4.86 (1) | | 0.0 (0)

0

### A=170, B=85, DIR=X, OE=H -> A=170, B=85: PASS

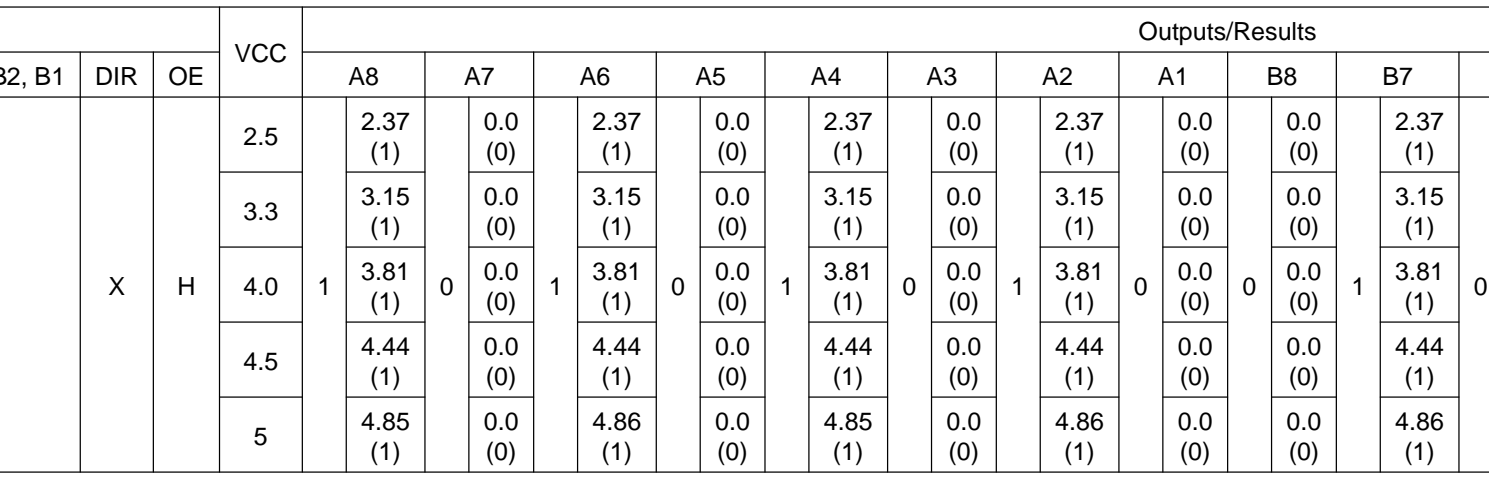
[picture p85: figure]
VCC; Outputs/Results

A8, A7, A6, A5, A4, A3, A2, A1 B8, B7, B6, B5, B4, B3, B2, B1 | DIR | OE | A8 | A7 | A6 | A5 | A4 | A3 | A2 | A1 | B8 | B7 | B6 | B5 | B4 | B3 | B2 | B1
