worthleychristopher-dev/IC-Test-Fixture-Capstone/test_results/hc_results/74hc688._short.pdf

## Pin Map

Pin Name | Pin | Pin Name | Pin
E | 1 | A0 | 2
A1 | 4 | A2 | 6
A3 | 8 | A4 | 11
A5 | 13 | A6 | 15
A7 | 17 | B0 | 3
B1 | 5 | B2 | 7
B3 | 9 | B4 | 12
B5 | 14 | B6 | 16
B7 | 18 | Y | 19

## Global Parameters

Parameter | Value
VCC Pin | 20
GND Pin | 10
VCC Voltage | 2.5, 3.3, 4.0, 4.5, 5
Input Low | 0.75, 0.99, 1.2, 1.35, 1.5
Input High | 1.75, 2.31, 2.8, 3.15, 3.5
Output Low | 0.3, 0.3, 0.3, 0.3, 0.3
Output High | 2.2, 3.0, 3.6, 4.1, 4.7

## Tests: IC PASS 19/19

### Comparator Disabled: PASS

Inputs | VCC | Outputs/Results
E | A7, A6, A5, A4, A3, A2, A1, A0 | B7, B6, B5, B4, B3, B2, B1, B0 | | Y
H | 0b00000000 | 0b00000000 | 2.5 | H | 2.37 (H)
| | | 3.3 | | 3.15 (H)
| | | 4.0 | | 3.81 (H)
| | | 4.5 | | 4.43 (H)
| | | 5 | | 4.85 (H)

### A=0, B=1 -> Y=H: PASS

Inputs | VCC | Outputs/Results
E | A7, A6, A5, A4, A3, A2, A1, A0 | B7, B6, B5, B4, B3, B2, B1, B0 | | Y
L | 0b00000000 | 0b00000001 | 2.5 | H | 2.37 (H)
| | | 3.3 | | 3.15 (H)
| | | 4.0 | | 3.81 (H)
| | | 4.5 | | 4.43 (H)
| | | 5 | | 4.85 (H)

### A=0, B=0 -> Y=L: PASS

Inputs | VCC | Outputs/Results
E | A7, A6, A5, A4, A3, A2, A1, A0 | B7, B6, B5, B4, B3, B2, B1, B0 | | Y
L | 0b00000000 | 0b00000000 | 2.5 | L | 0.0 (L)
| | | 3.3 | | 0.0 (L)
| | | 4.0 | | 0.0 (L)
| | | 4.5 | | 0.0 (L)
| | | 5 | | 0.0 (L)

### A=2, B=1 -> Y=H: PASS

Inputs | VCC | Outputs/Results
E | A7, A6, A5, A4, A3, A2, A1, A0 | B7, B6, B5, B4, B3, B2, B1, B0 | | Y
L | 0b00000010 | 0b00000001 | 2.5 | H | 2.37 (H)
| | | 3.3 | | 3.15 (H)
| | | 4.0 | | 3.81 (H)
| | | 4.5 | | 4.43 (H)
| | | 5 | | 4.85 (H)

### A=2, B=2 -> Y=L: PASS

Inputs | VCC | Outputs/Results
E | A7, A6, A5, A4, A3, A2, A1, A0 | B7, B6, B5, B4, B3, B2, B1, B0 | | Y
L | 0b00000010 | 0b00000010 | 2.5 | L | 0.0 (L)
| | | 3.3 | | 0.0 (L)
| | | 4.0 | | 0.0 (L)
| | | 4.5 | | 0.0 (L)
| | | 5 | | 0.0 (L)

### A=2, B=4 -> Y=H: PASS

Inputs | VCC | Outputs/Results
E | A7, A6, A5, A4, A3, A2, A1, A0 | B7, B6, B5, B4, B3, B2, B1, B0 | | Y
L | 0b00000010 | 0b00000100 | 2.5 | H | 2.37 (H)
| | | 3.3 | | 3.15 (H)
| | | 4.0 | | 3.81 (H)
| | | 4.5 | | 4.43 (H)
| | | 5 | | 4.85 (H)

### A=4, B=4 -> Y=L: PASS

Inputs | VCC | Outputs/Results
E | A7, A6, A5, A4, A3, A2, A1, A0 | B7, B6, B5, B4, B3, B2, B1, B0 | | Y
L | 0b00000100 | 0b00000100 | 2.5 | L | 0.0 (L)
| | | 3.3 | | 0.0 (L)
| | | 4.0 | | 0.0 (L)
| | | 4.5 | | 0.0 (L)
| | | 5 | | 0.0 (L)

### A=6, B=8 -> Y=H: PASS

Inputs | VCC | Outputs/Results
E | A7, A6, A5, A4, A3, A2, A1, A0 | B7, B6, B5, B4, B3, B2, B1, B0 | | Y
L | 0b00000110 | 0b00001000 | 2.5 | H | 2.37 (H)
| | | 3.3 | | 3.15 (H)
| | | 4.0 | | 3.81 (H)
| | | 4.5 | | 4.43 (H)
| | | 5 | | 4.85 (H)

### A=8, B=8 -> Y=L: PASS

Inputs | VCC | Outputs/Results
E | A7, A6, A5, A4, A3, A2, A1, A0 | B7, B6, B5, B4, B3, B2, B1, B0 | | Y
L | 0b00001000 | 0b00001000 | 2.5 | L | 0.0 (L)
| | | 3.3 | | 0.0 (L)
| | | 4.0 | | 0.0 (L)
| | | 4.5 | | 0.0 (L)
| | | 5 | | 0.0 (L)

### A=16, B=12 -> Y=H: PASS

Inputs | VCC | Outputs/Results
E | A7, A6, A5, A4, A3, A2, A1, A0 | B7, B6, B5, B4, B3, B2, B1, B0 | | Y
L | 0b00010000 | 0b00001100 | 2.5 | H | 2.37 (H)
| | | 3.3 | | 3.15 (H)
| | | 4.0 | | 3.81 (H)
| | | 4.5 | | 4.43 (H)
| | | 5 | | 4.85 (H)

### A=16, B=16 -> Y=L: PASS

Inputs | VCC | Outputs/Results
E | A7, A6, A5, A4, A3, A2, A1, A0 | B7, B6, B5, B4, B3, B2, B1, B0 | | Y
L | 0b00010000 | 0b00010000 | 2.5 | L | 0.0 (L)
| | | 3.3 | | 0.0 (L)
| | | 4.0 | | 0.0 (L)
| | | 4.5 | | 0.0 (L)
| | | 5 | | 0.0 (L)

### A=31, B=32 -> Y=H: PASS

Inputs | VCC | Outputs/Results
E | A7, A6, A5, A4, A3, A2, A1, A0 | B7, B6, B5, B4, B3, B2, B1, B0 | | Y
L | 0b00011111 | 0b00100000 | 2.5 | H | 2.37 (H)
| | | 3.3 | | 3.15 (H)
| | | 4.0 | | 3.81 (H)
| | | 4.5 | | 4.43 (H)
| | | 5 | | 4.85 (H)

### A=32, B=32 -> Y=L: PASS

Inputs | VCC | Outputs/Results
E | A7, A6, A5, A4, A3, A2, A1, A0 | B7, B6, B5, B4, B3, B2, B1, B0 | | Y
L | 0b00100000 | 0b00100000 | 2.5 | L | 0.0 (L)
| | | 3.3 | | 0.0 (L)
| | | 4.0 | | 0.0 (L)
| | | 4.5 | | 0.0 (L)
| | | 5 | | 0.0 (L)

### A=32, B=64 -> Y=H: PASS

Inputs | VCC | Outputs/Results
E | A7, A6, A5, A4, A3, A2, A1, A0 | B7, B6, B5, B4, B3, B2, B1, B0 | | Y
L | 0b00100000 | 0b01000000 | 2.5 | H | 2.37 (H)
| | | 3.3 | | 3.15 (H)
| | | 4.0 | | 3.81 (H)
| | | 4.5 | | 4.43 (H)
| | | 5 | | 4.85 (H)

### A=64, B=64 -> Y=L: PASS

Inputs | VCC | Outputs/Results
E | A7, A6, A5, A4, A3, A2, A1, A0 | B7, B6, B5, B4, B3, B2, B1, B0 | | Y
L | 0b01000000 | 0b01000000 | 2.5 | L | 0.0 (L)
| | | 3.3 | | 0.0 (L)
| | | 4.0 | | 0.0 (L)
| | | 4.5 | | 0.0 (L)
| | | 5 | | 0.0 (L)

### A=11, B=128 -> Y=H: PASS

Inputs | VCC | Outputs/Results
E | A7, A6, A5, A4, A3, A2, A1, A0 | B7, B6, B5, B4, B3, B2, B1, B0 | | Y
L | 0b00001011 | 0b10000000 | 2.5 | H | 2.37 (H)
| | | 3.3 | | 3.15 (H)
| | | 4.0 | | 3.81 (H)
| | | 4.5 | | 4.43 (H)
| | | 5 | | 4.85 (H)

### A=128, B=128 -> Y=H: PASS

Inputs | VCC | Outputs/Results
E | A7, A6, A5, A4, A3, A2, A1, A0 | B7, B6, B5, B4, B3, B2, B1, B0 | | Y
L | 0b10000000 | 0b10000000 | 2.5 | L | 0.0 (L)
| | | 3.3 | | 0.0 (L)
| | | 4.0 | | 0.0 (L)
| | | 4.5 | | 0.0 (L)
| | | 5 | | 0.0 (L)

### A=255, B=254 -> Y=H: PASS

Inputs | VCC | Outputs/Results
E | A7, A6, A5, A4, A3, A2, A1, A0 | B7, B6, B5, B4, B3, B2, B1, B0 | | Y
L | 0b11111111 | 0b11111110 | 2.5 | H | 2.37 (H)
| | | 3.3 | | 3.15 (H)
| | | 4.0 | | 3.81 (H)
| | | 4.5 | | 4.43 (H)
| | | 5 | | 4.85 (H)

### A=170, B=85 -> Y=H: PASS

Inputs | VCC | Outputs/Results
E | A7, A6, A5, A4, A3, A2, A1, A0 | B7, B6, B5, B4, B3, B2, B1, B0 | | Y
L | 0b10101010 | 0b01010101 | 2.5 | H | 2.37 (H)
| | | 3.3 | | 3.15 (H)
| | | 4.0 | | 3.81 (H)
| | | 4.5 | | 4.43 (H)
| | | 5 | | 4.85 (H)
