worthleychristopher-dev/IC-Test-Fixture-Capstone/test_results/hct_results/74hct245_short.pdf

## Pin Map

Pin Name | Pin | Pin Name | Pin
DIR | 1 | OE | 19
A1 | 2 | A2 | 3
A3 | 4 | A4 | 5
A5 | 6 | A6 | 7
A7 | 8 | A8 | 9
B1 | 18 | B2 | 17
B3 | 16 | B4 | 15
B5 | 14 | B6 | 13
B7 | 12 | B8 | 11

## Global Parameters

Parameter | Value
VCC Pin | 20
GND Pin | 10
VCC Voltage | 5
Input Low | 0.8
Input High | 2
Output Low | 0.33
Output High | 3.84

## Tests: IC PASS 19/19

### A=0, DIR=H, OE=L -> B=0: PASS

Inputs | Outputs/Results
A8, A7, A6, A5, A4, A3, A2, A1 | DIR | OE | B8 | B7 | B6 | B5 | B4 | B3 | B2 | B1
0b00000000 | H | L | 0 | 0.0 (0) 0 | | 0.0 (0) 0 | | 0.0 (0) 0 | | 0.0 (0) 0 | 0.0 (0) 0 | 0.0 (0) 0 | 0.0 (0) 0 | 0.0 (0)

### A=1, DIR=H, OE=L -> B=1: PASS

Inputs | Outputs/Results
A8, A7, A6, A5, A4, A3, A2, A1 | DIR | OE | B8 | B7 | B6 | B5 | B4 | B3 | B2 | B1
0b00000001 | H | L | 0 | 0.0 (0) 0 | | 0.0 (0) 0 | | 0.0 (0) 0 | | 0.0 (0) 0 | 0.0 (0) 0 | 0.0 (0) 0 | 0.0 (0) 1 | 4.86 (1)

### A=2, DIR=H, OE=L -> B=2: PASS

Inputs | Outputs/Results
A8, A7, A6, A5, A4, A3, A2, A1 | DIR | OE | B8 | B7 | B6 | B5 | B4 | B3 | B2 | B1
0b00000010 | H | L | 0 | 0.0 (0) 0 | | 0.0 (0) 0 | | 0.0 (0) 0 | | 0.0 (0) 0 | 0.0 (0) 0 | 0.0 (0) 1 | 4.86 (1) 0 | 0.0 (0)

### A=4, DIR=H, OE=L -> B=4: PASS

Inputs | Outputs/Results
A8, A7, A6, A5, A4, A3, A2, A1 | DIR | OE | B8 | B7 | B6 | B5 | B4 | B3 | B2 | B1
0b00000100 | H | L | 0 | 0.0 (0) 0 | | 0.0 (0) 0 | | 0.0 (0) 0 | | 0.0 (0) 0 | 0.0 (0) 1 | 4.85 (1) 0 | 0.0 (0) 0 | 0.0 (0)

### A=8, DIR=H, OE=L -> B=8: PASS

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
(0) 0

### A=170, B=85, DIR=X, OE=H -> A=170, B=85: PASS

Inputs; Outputs/Results

A8, A7, A6, A5, A4, A3, A2, A1 B8, B7, B6, B5, B4, B3, B2, B1 | DIR | OE | A8 | A7 | A6 | A5 | A4 | A3 | A2 | A1 | B8 | B7 | B6 | B5 | B4 | B3 | B2 | B1
(0) 1
