worthleychristopher-dev/IC-Test-Fixture-Capstone/test_results/hc_results/74hc138.pdf

## Pin Map

Pin Name | Pin | Pin Name | Pin
A | 1 | B | 2
C | 3 | G2A | 4
G2B | 5 | G1 | 6
Y7 | 7 | Y6 | 13
Y5 | 14 | Y4 | 15
Y3 | 16 | Y2 | 17
Y1 | 18 | Y0 | 19

## Global Parameters

Parameter | Value
VCC Pin | 20
GND Pin | 8
VCC Voltage | 2.5, 3.3, 4.0, 4.5, 5
Input Low | 0.75, 0.99, 1.2, 1.35, 1.5
Input High | 1.75, 2.31, 2.8, 3.15, 3.5
Output Low | 0.3, 0.3, 0.3, 0.3, 0.3
Output High | 2.2, 3.0, 3.6, 4.1, 4.7

## Tests: IC PASS 11/11

### Active Low G2A: PASS

Inputs | VCC | Outputs/Results
G1, G2A, G2B | C, B, A | | Y0 | Y1 | Y2 | Y3 | Y4 | Y5 | Y6 | Y7
X, H, X | X, X, X | 2.5 | H | 2.37 (H) | H | 2.37 (H) | H | 2.37 (H) | H | 2.37 (H) | H | 2.37 (H) | H | 2.37 (H) | H | 2.37 (H) | H | 2.37 (H)
| | 3.3 | | 3.16 (H) | | 3.16 (H) | | 3.16 (H) | | 3.16 (H) | | 3.16 (H) | | 3.16 (H) | | 3.16 (H) | | 3.16 (H)
| | 4.0 | | 3.81 (H) | | 3.81 (H) | | 3.81 (H) | | 3.81 (H) | | 3.81 (H) | | 3.81 (H) | | 3.81 (H) | | 3.81 (H)
| | 4.5 | | 4.44 (H) | | 4.44 (H) | | 4.44 (H) | | 4.44 (H) | | 4.44 (H) | | 4.44 (H) | | 4.44 (H) | | 4.44 (H)
| | 5 | | 4.87 (H) | | 4.87 (H) | | 4.87 (H) | | 4.87 (H) | | 4.87 (H) | | 4.87 (H) | | 4.87 (H) | | 4.87 (H)

### Active Low G2B: PASS

Inputs | VCC | Outputs/Results
G1, G2A, G2B | C, B, A | | Y0 | Y1 | Y2 | Y3 | Y4 | Y5 | Y6 | Y7
X, X, H | X, X, X | 2.5 | H | 2.37 (H) | H | 2.37 (H) | H | 2.37 (H) | H | 2.37 (H) | H | 2.37 (H) | H | 2.37 (H) | H | 2.37 (H) | H | 2.37 (H)
| | 3.3 | | 3.16 (H) | | 3.16 (H) | | 3.16 (H) | | 3.16 (H) | | 3.16 (H) | | 3.16 (H) | | 3.16 (H) | | 3.16 (H)
| | 4.0 | | 3.81 (H) | | 3.81 (H) | | 3.81 (H) | | 3.81 (H) | | 3.81 (H) | | 3.81 (H) | | 3.81 (H) | | 3.81 (H)
| | 4.5 | | 4.43 (H) | | 4.44 (H) | | 4.43 (H) | | 4.44 (H) | | 4.44 (H) | | 4.44 (H) | | 4.44 (H) | | 4.44 (H)
| | 5 | | 4.87 (H) | | 4.87 (H) | | 4.87 (H) | | 4.87 (H) | | 4.87 (H) | | 4.87 (H) | | 4.87 (H) | | 4.87 (H)

### Low G1: PASS

Inputs | VCC | Outputs/Results
G1, G2A, G2B | C, B, A | | Y0 | Y1 | Y2 | Y3 | Y4 | Y5 | Y6 | Y7
L, X, X | X, X, X | 2.5 | H | 2.37 (H) | H | 2.37 (H) | H | 2.37 (H) | H | 2.37 (H) | H | 2.37 (H) | H | 2.37 (H) | H | 2.37 (H) | H | 2.37 (H)
| | 3.3 | | 3.16 (H) | | 3.16 (H) | | 3.16 (H) | | 3.16 (H) | | 3.15 (H) | | 3.16 (H) | | 3.16 (H) | | 3.16 (H)
| | 4.0 | | 3.81 (H) | | 3.81 (H) | | 3.81 (H) | | 3.81 (H) | | 3.81 (H) | | 3.81 (H) | | 3.81 (H) | | 3.81 (H)
| | 4.5 | | 4.44 (H) | | 4.43 (H) | | 4.44 (H) | | 4.44 (H) | | 4.44 (H) | | 4.44 (H) | | 4.44 (H) | | 4.44 (H)
| | 5 | | 4.87 (H) | | 4.87 (H) | | 4.87 (H) | | 4.87 (H) | | 4.87 (H) | | 4.87 (H) | | 4.87 (H) | | 4.87 (H)

### Output Y0: PASS

Inputs | VCC | Outputs/Results
G1, G2A, G2B | C, B, A | | Y0 | Y1 | Y2 | Y3 | Y4 | Y5 | Y6 | Y7
H, L, L | 0b000 | 2.5 | L | 0.0 (L) | H | 2.37 (H) | H | 2.37 (H) | H | 2.37 (H) | H | 2.37 (H) | H | 2.37 (H) | H | 2.37 (H) | H | 2.37 (H)
| | 3.3 | | 0.0 (L) | | 3.16 (H) | | 3.16 (H) | | 3.16 (H) | | 3.16 (H) | | 3.16 (H) | | 3.16 (H) | | 3.16 (H)
| | 4.0 | | 0.0 (L) | | 3.81 (H) | | 3.81 (H) | | 3.81 (H) | | 3.81 (H) | | 3.81 (H) | | 3.82 (H) | | 3.81 (H)
| | 4.5 | | 0.0 (L) | | 4.44 (H) | | 4.44 (H) | | 4.44 (H) | | 4.44 (H) | | 4.44 (H) | | 4.44 (H) | | 4.44 (H)
| | 5 | | 0.0 (L) | | 4.87 (H) | | 4.87 (H) | | 4.87 (H) | | 4.87 (H) | | 4.87 (H) | | 4.87 (H) | | 4.87 (H)

### Output Y1: PASS

Inputs | VCC | Outputs/Results
G1, G2A, G2B | C, B, A | | Y0 | Y1 | Y2 | Y3 | Y4 | Y5 | Y6 | Y7
H, L, L | 0b001 | 2.5 | H | 2.37 (H) | L | 0.0 (L) | H | 2.37 (H) | H | 2.37 (H) | H | 2.37 (H) | H | 2.37 (H) | H | 2.37 (H) | H | 2.37 (H)
| | 3.3 | | 3.16 (H) | | 0.0 (L) | | 3.16 (H) | | 3.16 (H) | | 3.16 (H) | | 3.16 (H) | | 3.16 (H) | | 3.16 (H)
| | 4.0 | | 3.81 (H) | | 0.0 (L) | | 3.81 (H) | | 3.81 (H) | | 3.81 (H) | | 3.81 (H) | | 3.81 (H) | | 3.81 (H)
| | 4.5 | | 4.44 (H) | | 0.0 (L) | | 4.44 (H) | | 4.44 (H) | | 4.44 (H) | | 4.44 (H) | | 4.44 (H) | | 4.44 (H)
| | 5 | | 4.87 (H) | | 0.0 (L) | | 4.87 (H) | | 4.87 (H) | | 4.87 (H) | | 4.87 (H) | | 4.87 (H) | | 4.87 (H)

### Output Y2: PASS

Inputs | VCC | Outputs/Results
G1, G2A, G2B | C, B, A | | Y0 | Y1 | Y2 | Y3 | Y4 | Y5 | Y6 | Y7
H, L, L | 0b010 | 2.5 | H | 2.37 (H) | H | 2.37 (H) | L | 0.0 (L) | H | 2.37 (H) | H | 2.37 (H) | H | 2.37 (H) | H | 2.37 (H) | H | 2.37 (H)
| | 3.3 | | 3.16 (H) | | 3.16 (H) | | 0.0 (L) | | 3.16 (H) | | 3.16 (H) | | 3.16 (H) | | 3.16 (H) | | 3.16 (H)
| | 4.0 | | 3.81 (H) | | 3.81 (H) | | 0.0 (L) | | 3.81 (H) | | 3.81 (H) | | 3.81 (H) | | 3.81 (H) | | 3.81 (H)
| | 4.5 | | 4.44 (H) | | 4.44 (H) | | 0.0 (L) | | 4.44 (H) | | 4.44 (H) | | 4.44 (H) | | 4.44 (H) | | 4.44 (H)
| | 5 | | 4.87 (H) | | 4.87 (H) | | 0.0 (L) | | 4.87 (H) | | 4.87 (H) | | 4.87 (H) | | 4.87 (H) | | 4.87 (H)

### Output Y3: PASS

Inputs | VCC | Outputs/Results
G1, G2A, G2B | C, B, A | | Y0 | Y1 | Y2 | Y3 | Y4 | Y5 | Y6 | Y7
H, L, L | 0b011 | 2.5 | H | 2.37 (H) | H | 2.37 (H) | H | 2.37 (H) | L | 0.0 (L) | H | 2.37 (H) | H | 2.37 (H) | H | 2.37 (H) | H | 2.37 (H)
| | 3.3 | | 3.16 (H) | | 3.16 (H) | | 3.16 (H) | | 0.0 (L) | | 3.16 (H) | | 3.16 (H) | | 3.16 (H) | | 3.16 (H)
| | 4.0 | | 3.81 (H) | | 3.81 (H) | | 3.81 (H) | | 0.0 (L) | | 3.81 (H) | | 3.82 (H) | | 3.81 (H) | | 3.81 (H)
| | 4.5 | | 4.44 (H) | | 4.44 (H) | | 4.44 (H) | | 0.0 (L) | | 4.44 (H) | | 4.44 (H) | | 4.44 (H) | | 4.44 (H)
| | 5 | | 4.87 (H) | | 4.87 (H) | | 4.87 (H) | | 0.0 (L) | | 4.87 (H) | | 4.87 (H) | | 4.87 (H) | | 4.87 (H)

### Output Y4: PASS

Inputs | VCC | Outputs/Results
G1, G2A, G2B | C, B, A | | Y0 | Y1 | Y2 | Y3 | Y4 | Y5 | Y6 | Y7
H, L, L | 0b100 | 2.5 | H | 2.37 (H) | H | 2.37 (H) | H | 2.37 (H) | H | 2.37 (H) | L | 0.0 (L) | H | 2.37 (H) | H | 2.37 (H) | H | 2.37 (H)
| | 3.3 | | 3.16 (H) | | 3.16 (H) | | 3.16 (H) | | 3.16 (H) | | 0.0 (L) | | 3.16 (H) | | 3.16 (H) | | 3.16 (H)
| | 4.0 | | 3.81 (H) | | 3.81 (H) | | 3.81 (H) | | 3.81 (H) | | 0.0 (L) | | 3.81 (H) | | 3.82 (H) | | 3.81 (H)
| | 4.5 | | 4.44 (H) | | 4.44 (H) | | 4.44 (H) | | 4.44 (H) | | 0.0 (L) | | 4.44 (H) | | 4.44 (H) | | 4.44 (H)
| | 5 | | 4.87 (H) | | 4.87 (H) | | 4.87 (H) | | 4.87 (H) | | 0.0 (L) | | 4.87 (H) | | 4.87 (H) | | 4.87 (H)

### Output Y5: PASS

Inputs | VCC | Outputs/Results
G1, G2A, G2B | C, B, A | | Y0 | Y1 | Y2 | Y3 | Y4 | Y5 | Y6 | Y7
H, L, L | 0b101 | 2.5 | H | 2.37 (H) | H | 2.37 (H) | H | 2.37 (H) | H | 2.37 (H) | H | 2.37 (H) | L | 0.0 (L) | H | 2.37 (H) | H | 2.37 (H)
| | 3.3 | | 3.16 (H) | | 3.16 (H) | | 3.16 (H) | | 3.16 (H) | | 3.16 (H) | | 0.0 (L) | | 3.16 (H) | | 3.16 (H)
| | 4.0 | | 3.81 (H) | | 3.81 (H) | | 3.81 (H) | | 3.81 (H) | | 3.81 (H) | | 0.0 (L) | | 3.82 (H) | | 3.82 (H)
| | 4.5 | | 4.44 (H) | | 4.44 (H) | | 4.44 (H) | | 4.44 (H) | | 4.44 (H) | | 0.0 (L) | | 4.44 (H) | | 4.44 (H)
| | 5 | | 4.88 (H) | | 4.88 (H) | | 4.87 (H) | | 4.87 (H) | | 4.88 (H) | | 0.0 (L) | | 4.88 (H) | | 4.88 (H)

### Output Y6: PASS

Inputs | VCC | Outputs/Results
G1, G2A, G2B | C, B, A | | Y0 | Y1 | Y2 | Y3 | Y4 | Y5 | Y6 | Y7
H, L, L | 0b110 | 2.5 | H | 2.37 (H) | H | 2.37 (H) | H | 2.37 (H) | H | 2.37 (H) | H | 2.37 (H) | H | 2.37 (H) | L | 0.0 (L) | H | 2.37 (H)
| | 3.3 | | 3.16 (H) | | 3.16 (H) | | 3.16 (H) | | 3.16 (H) | | 3.16 (H) | | 3.16 (H) | | 0.0 (L) | | 3.16 (H)
| | 4.0 | | 3.81 (H) | | 3.81 (H) | | 3.81 (H) | | 3.81 (H) | | 3.81 (H) | | 3.81 (H) | | 0.0 (L) | | 3.82 (H)
| | 4.5 | | 4.44 (H) | | 4.44 (H) | | 4.44 (H) | | 4.44 (H) | | 4.44 (H) | | 4.44 (H) | | 0.0 (L) | | 4.44 (H)
| | 5 | | 4.87 (H) | | 4.87 (H) | | 4.87 (H) | | 4.87 (H) | | 4.87 (H) | | 4.87 (H) | | 0.0 (L) | | 4.88 (H)

### Output Y7: PASS

Inputs | VCC | Outputs/Results
G1, G2A, G2B | C, B, A | | Y0 | Y1 | Y2 | Y3 | Y4 | Y5 | Y6 | Y7
H, L, L | 0b111 | 2.5 | H | 2.37 (H) | H | 2.37 (H) | H | 2.37 (H) | H | 2.37 (H) | H | 2.37 (H) | H | 2.37 (H) | H | 2.37 (H) | L | 0.0 (L)
| | 3.3 | | 3.16 (H) | | 3.16 (H) | | 3.16 (H) | | 3.16 (H) | | 3.16 (H) | | 3.16 (H) | | 3.16 (H) | | 0.0 (L)
| | 4.0 | | 3.82 (H) | | 3.82 (H) | | 3.82 (H) | | 3.82 (H) | | 3.82 (H) | | 3.81 (H) | | 3.81 (H) | | 0.0 (L)
| | 4.5 | | 4.44 (H) | | 4.44 (H) | | 4.44 (H) | | 4.44 (H) | | 4.44 (H) | | 4.44 (H) | | 4.44 (H) | | 0.0 (L)
| | 5 | | 4.88 (H) | | 4.87 (H) | | 4.87 (H) | | 4.87 (H) | | 4.87 (H) | | 4.87 (H) | | 4.87 (H) | | 0.0 (L)
