worthleychristopher-dev/IC-Test-Fixture-Capstone/test_results/hc_results/74hc153.pdf

## Pin Map

Pin Name | Pin | Pin Name | Pin
1E | 1 | S1 | 2
1I3 | 3 | 1I2 | 4
1I1 | 5 | 1I0 | 6
1Y | 7 | 2Y | 13
2I0 | 14 | 2I1 | 15
2I2 | 16 | 2I3 | 17
S0 | 18 | 2E | 19

## Global Parameters

Parameter | Value
VCC Pin | 20
GND Pin | 8
VCC Voltage | 2.5, 3.3, 4.0, 4.5, 5
Input Low | 0.75, 0.99, 1.2, 1.35, 1.5
Input High | 1.75, 2.31, 2.8, 3.15, 3.5
Output Low | 0.3, 0.3, 0.3, 0.3, 0.3
Output High | 2.2, 3.0, 3.6, 4.1, 4.7

## Tests: IC PASS 2/2

### Mux 1: PASS

Inputs
VCC

Outputs/Results
1E | S1 X | S0 X | 1I3 X | 1I2 X | 1I1 X | 1I0 X | 2.5 | L | 1Y H 0.0 (L)
| | | | | | | 3.3 | | 0.0 (L)
| | | | | | | 4.0 | | 0.0 (L)
| | | | | | | 4.5 | | 0.0 (L)
| | | | | | | 5 | | 0.0 (L)
L | L | L | X | X | X | L | 2.5 | L | 0.0 (L)
| | | | | | | 3.3 | | 0.0 (L)
| | | | | | | 4.0 | | 0.0 (L)
| | | | | | | 4.5 | | 0.0 (L)
| | | | | | | 5 | | 0.0 (L)
L | L | L | X | X | X | H | 2.5 | H | 2.37 (H)
| | | | | | | 3.3 | | 3.15 (H)
| | | | | | | 4.0 | | 3.81 (H)
| | | | | | | 4.5 | | 4.44 (H)
| | | | | | | 5 | | 4.87 (H)
L | L | H | X | X | L | X | 2.5 | L | 0.0 (L)
| | | | | | | 3.3 | | 0.0 (L)
| | | | | | | 4.0 | | 0.0 (L)
| | | | | | | 4.5 | | 0.0 (L)
| | | | | | | 5 | | 0.0 (L)

Inputs
VCC

Outputs/Results
1E | S1 L | S0 H | 1I3 X | 1I2 X | 1I1 H | 1I0 X | 2.5 | H | 1Y L 2.37 (H)
| | | | | | | 3.3 | | 3.15 (H)
| | | | | | | 4.0 | | 3.81 (H)
| | | | | | | 4.5 | | 4.44 (H)
| | | | | | | 5 | | 4.87 (H)
L | H | L | X | L | X | X | 2.5 | L | 0.0 (L)
| | | | | | | 3.3 | | 0.0 (L)
| | | | | | | 4.0 | | 0.0 (L)
| | | | | | | 4.5 | | 0.0 (L)
| | | | | | | 5 | | 0.0 (L)
L | H | L | X | H | X | X | 2.5 | H | 2.37 (H)
| | | | | | | 3.3 | | 3.15 (H)
| | | | | | | 4.0 | | 3.81 (H)
| | | | | | | 4.5 | | 4.44 (H)
| | | | | | | 5 | | 4.87 (H)
L | H | H | L | X | X | X | 2.5 | L | 0.0 (L)
| | | | | | | 3.3 | | 0.0 (L)
| | | | | | | 4.0 | | 0.0 (L)
| | | | | | | 4.5 | | 0.0 (L)
| | | | | | | 5 | | 0.0 (L)

Inputs | VCC | Outputs/Results
1E | S1 | S0 | 1I3 | 1I2 | 1I1 | 1I0 | | 1Y
L | H | H | H | X | X | X | 2.5 | H | 2.37 (H)
| | | | | | | 3.3 | | 3.15 (H)
| | | | | | | 4.0 | | 3.81 (H)
| | | | | | | 4.5 | | 4.43 (H)
| | | | | | | 5 | | 4.87 (H)

### Mux 2: PASS

Inputs | VCC | Outputs/Results
2E | S1 | S0 | 2I3 | 2I2 | 2I1 | 2I0 | | 2Y
H | X | X | X | X | X | X | 2.5 | L | 0.0 (L)
| | | | | | | 3.3 | | 0.0 (L)
| | | | | | | 4.0 | | 0.0 (L)
| | | | | | | 4.5 | | 0.0 (L)
| | | | | | | 5 | | 0.0 (L)
L | L | L | X | X | X | L | 2.5 | L | 0.0 (L)
| | | | | | | 3.3 | | 0.0 (L)
| | | | | | | 4.0 | | 0.0 (L)
| | | | | | | 4.5 | | 0.0 (L)
| | | | | | | 5 | | 0.0 (L)

Inputs
VCC

Outputs/Results
2E | S1 L | S0 L | 2I3 X | 2I2 X | 2I1 X | 2I0 H | 2.5 | H | 2Y L 2.37 (H)
| | | | | | | 3.3 | | 3.15 (H)
| | | | | | | 4.0 | | 3.81 (H)
| | | | | | | 4.5 | | 4.44 (H)
| | | | | | | 5 | | 4.87 (H)
L | L | H | X | X | L | X | 2.5 | L | 0.0 (L)
| | | | | | | 3.3 | | 0.0 (L)
| | | | | | | 4.0 | | 0.0 (L)
| | | | | | | 4.5 | | 0.0 (L)
| | | | | | | 5 | | 0.0 (L)
L | L | H | X | X | H | X | 2.5 | H | 2.37 (H)
| | | | | | | 3.3 | | 3.15 (H)
| | | | | | | 4.0 | | 3.81 (H)
| | | | | | | 4.5 | | 4.44 (H)
| | | | | | | 5 | | 4.87 (H)
L | H | L | X | L | X | X | 2.5 | L | 0.0 (L)
| | | | | | | 3.3 | | 0.0 (L)
| | | | | | | 4.0 | | 0.0 (L)
| | | | | | | 4.5 | | 0.0 (L)
| | | | | | | 5 | | 0.0 (L)

Inputs
VCC

Outputs/Results
2E | S1 H | S0 L | 2I3 X | 2I2 H | 2I1 X | 2I0 X | 2.5 | H | 2Y L 2.37 (H)
| | | | | | | 3.3 | | 3.15 (H)
| | | | | | | 4.0 | | 3.81 (H)
| | | | | | | 4.5 | | 4.44 (H)
| | | | | | | 5 | | 4.87 (H)
L | H | H | L | X | X | X | 2.5 | L | 0.0 (L)
| | | | | | | 3.3 | | 0.0 (L)
| | | | | | | 4.0 | | 0.0 (L)
| | | | | | | 4.5 | | 0.0 (L)
| | | | | | | 5 | | 0.0 (L)
L | H | H | H | X | X | X | 2.5 | H | 2.37 (H)
| | | | | | | 3.3 | | 3.15 (H)
| | | | | | | 4.0 | | 3.81 (H)
| | | | | | | 4.5 | | 4.44 (H)
| | | | | | | 5 | | 4.87 (H)
