worthleychristopher-dev/IC-Test-Fixture-Capstone/test_results/hc_results/74hc244.pdf

## Global Parameters

Parameter | Value
VCC Pin | 20
GND Pin | 10
VCC Voltage | 2.5, 3.3, 4.0, 4.5, 5
Input Low | 0.75, 0.99, 1.2, 1.35, 1.5
Input High | 1.75, 2.31, 2.8, 3.15, 3.5
Output Low | 0.3, 0.3, 0.3, 0.3, 0.3
Output High | 2.2, 3.0, 3.6, 4.1, 4.7

## Tests: IC PASS 6/6

### Buffer 1 Disabled: PASS

Inputs | VCC | Outputs/Results
1 | 2, 4, 6, 8 | | 18 | 16 | 14 | 12
H | X | 2.5 | Z | 1.59 (Z) | Z | 1.59 (Z) | Z | 1.59 (Z) | Z | 1.59 (Z)
| | 3.3 | | 1.59 (Z) | | 1.59 (Z) | | 1.59 (Z) | | 1.59 (Z)
| | 4.0 | | 1.59 (Z) | | 1.59 (Z) | | 1.59 (Z) | | 1.59 (Z)
| | 4.5 | | 1.59 (Z) | | 1.59 (Z) | | 1.59 (Z) | | 1.59 (Z)
| | 5 | | 1.59 (Z) | | 1.59 (Z) | | 1.59 (Z) | | 1.59 (Z)

### Buffer 1 A=L -> Y=L: PASS

Inputs | VCC | Outputs/Results
1 | 2, 4, 6, 8 | | 18 | 16 | 14 | 12
L | L | 2.5 | L | 0.0 (L) | L | 0.0 (L) | L | 0.0 (L) | L | 0.0 (L)
| | 3.3 | | 0.0 (L) | | 0.0 (L) | | 0.0 (L) | | 0.0 (L)
| | 4.0 | | 0.0 (L) | | 0.0 (L) | | 0.0 (L) | | 0.0 (L)
| | 4.5 | | 0.0 (L) | | 0.0 (L) | | 0.0 (L) | | 0.0 (L)
| | 5 | | 0.0 (L) | | 0.0 (L) | | 0.0 (L) | | 0.0 (L)

### Buffer 1 A=H -> Y=H: PASS

Inputs | VCC | Outputs/Results
1 | 2, 4, 6, 8 | | 18 | 16 | 14 | 12
L | H | 2.5 | H | 2.36 (H) | H | 2.36 (H) | H | 2.36 (H) | H | 2.37 (H)
| | 3.3 | | 3.15 (H) | | 3.15 (H) | | 3.15 (H) | | 3.15 (H)
| | 4.0 | | 3.8 (H) | | 3.8 (H) | | 3.8 (H) | | 3.8 (H)
| | 4.5 | | 4.39 (H) | | 4.39 (H) | | 4.39 (H) | | 4.41 (H)
| | 5 | | 4.87 (H) | | 4.87 (H) | | 4.87 (H) | | 4.87 (H)

### Buffer 2 Disabled: PASS

Inputs | VCC | Outputs/Results
19 | 11, 13, 15, 17 | | 9 | 7 | 5 | 3
H | X | 2.5 | Z | 1.59 (Z) | Z | 1.59 (Z) | Z | 1.59 (Z) | Z | 1.59 (Z)
| | 3.3 | | 1.59 (Z) | | 1.59 (Z) | | 1.59 (Z) | | 1.59 (Z)
| | 4.0 | | 1.59 (Z) | | 1.59 (Z) | | 1.59 (Z) | | 1.59 (Z)
| | 4.5 | | 1.59 (Z) | | 1.59 (Z) | | 1.59 (Z) | | 1.59 (Z)
| | 5 | | 1.59 (Z) | | 1.59 (Z) | | 1.59 (Z) | | 1.59 (Z)

### Buffer 2 A=L -> Y=L: PASS

Inputs | VCC | Outputs/Results
19 | 11, 13, 15, 17 | | 9 | 7 | 5 | 3
L | L | 2.5 | L | 0.0 (L) | L | 0.0 (L) | L | 0.0 (L) | L | 0.0 (L)
| | 3.3 | | 0.0 (L) | | 0.0 (L) | | 0.0 (L) | | 0.0 (L)
| | 4.0 | | 0.0 (L) | | 0.0 (L) | | 0.0 (L) | | 0.0 (L)
| | 4.5 | | 0.0 (L) | | 0.0 (L) | | 0.0 (L) | | 0.0 (L)
| | 5 | | 0.0 (L) | | 0.0 (L) | | 0.0 (L) | | 0.0 (L)

### Buffer 2 A=H -> Y=H: PASS

Inputs | VCC | Outputs/Results
19 | 11, 13, 15, 17 | | 9 | 7 | 5 | 3
L | H | 2.5 | H | 2.36 (H) | H | 2.36 (H) | H | 2.36 (H) | H | 2.36 (H)
| | 3.3 | | 3.14 (H) | | 3.14 (H) | | 3.14 (H) | | 3.14 (H)
| | 4.0 | | 3.7 (H) | | 3.78 (H) | | 3.79 (H) | | 3.79 (H)
| | 4.5 | | 4.22 (H) | | 4.36 (H) | | 4.37 (H) | | 4.37 (H)
| | 5 | | 4.86 (H) | | 4.86 (H) | | 4.87 (H) | | 4.87 (H)
