worthleychristopher-dev/IC-Test-Fixture-Capstone/hardware/vref_circuits/TLV431_1_8v_E192.asc

C1: cap; 0.1µF
R1: res; 1130
R2: res; 2490
R3: res; 2490
R_Load_Test: res; 10000
U1: TLV431
V1: voltage; 5v
Named nets: 0, 1.8v_Ref
.tran 300
