worthleychristopher-dev/IC-Test-Fixture-Capstone/hardware/vref_circuits/TLV431_test_simulation.asc

C1: cap; 0.1µF
R1: res; 2629
R2: res; 1000
R3: res; 35
R_Load_Test: res; 10000
U1: TLV431
V1: voltage; 5v
Named nets: 0, 4.5v_Ref
.tran 300
