worthleychristopher-dev/IC-Test-Fixture-Capstone/firmware/STM32_main/Core/Inc/main.h

#define MAX_PINS        20
#define LINE_BUF_SIZE   512
#define VIP_BIN_MAX     64   // supports up to 32 bits + "0b" + null
