worthleychristopher-dev/IC-Test-Fixture-Capstone/firmware/STM32_main/Core/Inc/bist.h

/*
 * bist.h
 *
 *  Created on: Apr 23, 2026
 *      Author: worthc2
 */

#ifndef BIST_H
#define BIST_H

#ifdef __cplusplus
extern "C" {
#endif

void Run_BIST(void);

#ifdef __cplusplus
}
#endif

#endif /* BIST_H */
